okemessi/midimalletg/docs/block_diagram/block_diagram.png

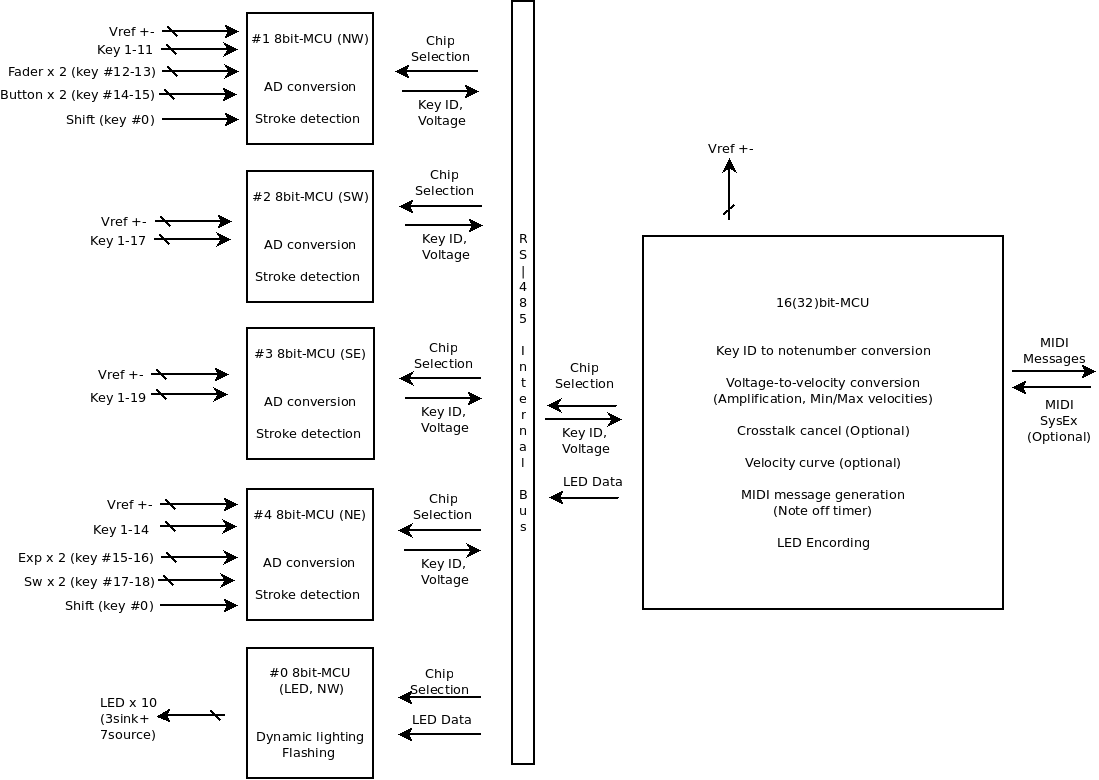
docs/block_diagram/block_diagram.png
