okemessi/midimalletg/docs/MCUs_pin_assign/chip0.png

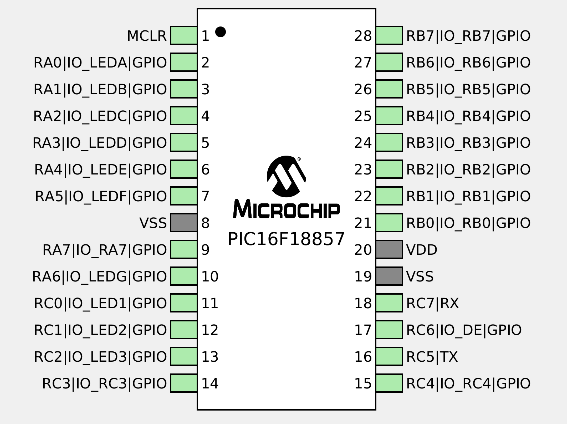
docs/MCUs_pin_assign/chip0.png
