okemessi/midimalletg/docs/MCUs_pin_assign/chip1.png

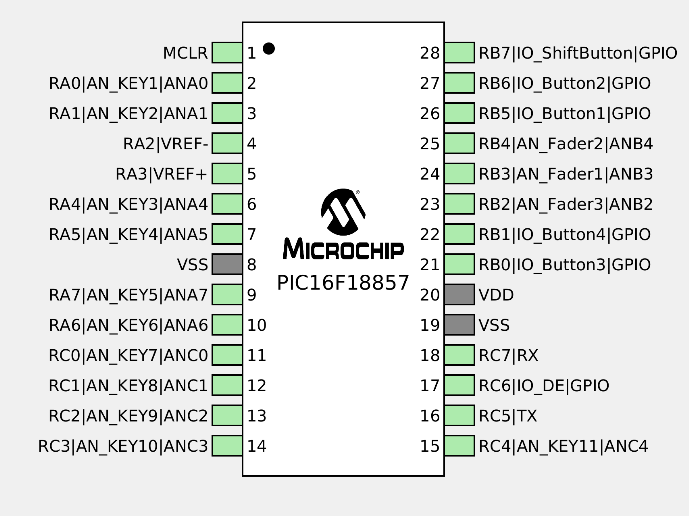
docs/MCUs_pin_assign/chip1.png
