okemessi/midimalletg/docs/MCUs_pin_assign/chipF.png

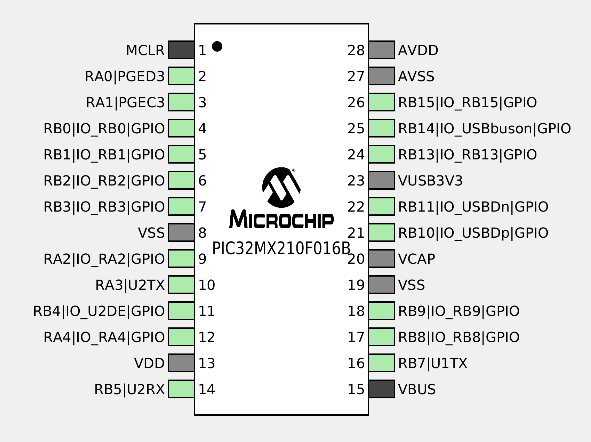
docs/MCUs_pin_assign/chipF.png
